SRB2149/SR-CRT/FPGA/SPI_to_CRT/src/gowin_dpb/gowin_dpb_tmp.v

//Copyright (C)2014-2024 Gowin Semiconductor Corporation.
//All rights reserved.
//File Title: Template file for instantiation
//Tool Version: V1.9.10.03 Education (64-bit)
//Part Number: GW1NR-LV9QN88PC6/I5
//Device: GW1NR-9
//Device Version: C
//Created Time: Sun May 10 15:20:16 2026

//Change the instance name and port connections to the signal names
//--------Copy here to design--------

    DPBSRAM your_instance_name(
        .douta(douta), //output [7:0] douta
        .doutb(doutb), //output [7:0] doutb
        .clka(clka), //input clka
        .ocea(ocea), //input ocea
        .cea(cea), //input cea
        .reseta(reseta), //input reseta
        .wrea(wrea), //input wrea
        .clkb(clkb), //input clkb
        .oceb(oceb), //input oceb
        .ceb(ceb), //input ceb
        .resetb(resetb), //input resetb
        .wreb(wreb), //input wreb
        .ada(ada), //input [14:0] ada
        .dina(dina), //input [7:0] dina
        .adb(adb), //input [14:0] adb
        .dinb(dinb) //input [7:0] dinb
    );

//--------Copy end-------------------
