SRB2149/SR-CRT/FPGA/CRT_Test/src/gowin_dpb/crt_frame_buffer_dpbsram.v

//Copyright (C)2014-2024 Gowin Semiconductor Corporation.
//All rights reserved.
//File Title: IP file
//Tool Version: V1.9.10.03 Education (64-bit)
//Part Number: GW1NR-LV9QN88PC6/I5
//Device: GW1NR-9
//Device Version: C
//Created Time: Mon Dec 15 19:14:27 2025

module CRT_FRAME_BUFFER_DPBSRAM (douta, doutb, clka, ocea, cea, reseta, wrea, clkb, oceb, ceb, resetb, wreb, ada, dina, adb, dinb);

output [7:0] douta;
output [7:0] doutb;
input clka;
input ocea;
input cea;
input reseta;
input wrea;
input clkb;
input oceb;
input ceb;
input resetb;
input wreb;
input [13:0] ada;
input [7:0] dina;
input [13:0] adb;
input [7:0] dinb;

wire [13:0] dpb_inst_0_douta_w;
wire [1:0] dpb_inst_0_douta;
wire [13:0] dpb_inst_0_doutb_w;
wire [1:0] dpb_inst_0_doutb;
wire [13:0] dpb_inst_1_douta_w;
wire [3:2] dpb_inst_1_douta;
wire [13:0] dpb_inst_1_doutb_w;
wire [3:2] dpb_inst_1_doutb;
wire [13:0] dpb_inst_2_douta_w;
wire [5:4] dpb_inst_2_douta;
wire [13:0] dpb_inst_2_doutb_w;
wire [5:4] dpb_inst_2_doutb;
wire [13:0] dpb_inst_3_douta_w;
wire [7:6] dpb_inst_3_douta;
wire [13:0] dpb_inst_3_doutb_w;
wire [7:6] dpb_inst_3_doutb;
wire [7:0] dpb_inst_4_douta_w;
wire [7:0] dpb_inst_4_douta;
wire [7:0] dpb_inst_4_doutb_w;
wire [7:0] dpb_inst_4_doutb;
wire dff_q_0;
wire dff_q_1;
wire cea_w;
wire ceb_w;
wire gw_gnd;

assign cea_w = ~wrea & cea;
assign ceb_w = ~wreb & ceb;
assign gw_gnd = 1'b0;

DPB dpb_inst_0 (
    .DOA({dpb_inst_0_douta_w[13:0],dpb_inst_0_douta[1:0]}),
    .DOB({dpb_inst_0_doutb_w[13:0],dpb_inst_0_doutb[1:0]}),
    .CLKA(clka),
    .OCEA(ocea),
    .CEA(cea),
    .RESETA(reseta),
    .WREA(wrea),
    .CLKB(clkb),
    .OCEB(oceb),
    .CEB(ceb),
    .RESETB(resetb),
    .WREB(wreb),
    .BLKSELA({gw_gnd,gw_gnd,ada[13]}),
    .BLKSELB({gw_gnd,gw_gnd,adb[13]}),
    .ADA({ada[12:0],gw_gnd}),
    .DIA({gw_gnd,gw_gnd,gw_gnd,gw_gnd,gw_gnd,gw_gnd,gw_gnd,gw_gnd,gw_gnd,gw_gnd,gw_gnd,gw_gnd,gw_gnd,gw_gnd,dina[1:0]}),
    .ADB({adb[12:0],gw_gnd}),
    .DIB({gw_gnd,gw_gnd,gw_gnd,gw_gnd,gw_gnd,gw_gnd,gw_gnd,gw_gnd,gw_gnd,gw_gnd,gw_gnd,gw_gnd,gw_gnd,gw_gnd,dinb[1:0]})
);

defparam dpb_inst_0.READ_MODE0 = 1'b0;
defparam dpb_inst_0.READ_MODE1 = 1'b0;
defparam dpb_inst_0.WRITE_MODE0 = 2'b00;
defparam dpb_inst_0.WRITE_MODE1 = 2'b00;
defparam dpb_inst_0.BIT_WIDTH_0 = 2;
defparam dpb_inst_0.BIT_WIDTH_1 = 2;
defparam dpb_inst_0.BLK_SEL_0 = 3'b000;
defparam dpb_inst_0.BLK_SEL_1 = 3'b000;
defparam dpb_inst_0.RESET_MODE = "ASYNC";
defparam dpb_inst_0.INIT_RAM_00 = 256'h000000004000000000000000001000000000000000000FFFFFFFFFFFFFFFFFFF;
defparam dpb_inst_0.INIT_RAM_01 = 256'h0000000000000000180000000000000000040000000000000000010000000000;
defparam dpb_inst_0.INIT_RAM_02 = 256'h0000001000000000000000000400000000000000000900000000000000000150;
defparam dpb_inst_0.INIT_RAM_03 = 256'h0000000000000004800000000000000001000000000000000000400000000000;
defparam dpb_inst_0.INIT_RAM_04 = 256'h0000040000000000000000010000000000000000084000000000000000011100;
defparam dpb_inst_0.INIT_RAM_05 = 256'h0000000000000108000000000000000040000000000000000010000000000000;
defparam dpb_inst_0.INIT_RAM_06 = 256'h0001000000000040000000400000000070000008100000000000000001041000;
defparam dpb_inst_0.INIT_RAM_07 = 256'h0010000000004080000000700000001000000000140000000400000000070000;
defparam dpb_inst_0.INIT_RAM_08 = 256'h00400000000F5800000010000000031E0000080400000000C780000101010000;
defparam dpb_inst_0.INIT_RAM_09 = 256'hFC0800000010080000070A0000000400000001E380000001000000007DE00000;
defparam dpb_inst_0.INIT_RAM_0A = 256'h10000000070E0000000400000001C28000000100000003F02000030040100000;
defparam dpb_inst_0.INIT_RAM_0B = 256'h1E0000400400800000C780000001000000003160000000400000001C78000000;
defparam dpb_inst_0.INIT_RAM_0C = 256'h0000000009000000010000000000800000004000000004000002001001000003;
defparam dpb_inst_0.INIT_RAM_0D = 256'h0000400100080000000000000040000000008000000010000000002000000004;
defparam dpb_inst_0.INIT_RAM_0E = 256'h0000000000000000400000000000000000100000000000000200040010000000;
defparam dpb_inst_0.INIT_RAM_0F = 256'h0040004000C00000000000001000000000000000000400000000000000000100;
defparam dpb_inst_0.INIT_RAM_10 = 256'h0000000000000010000000000000000004000000000000020001000000000000;
defparam dpb_inst_0.INIT_RAM_11 = 256'h400010000C002F40000000040000000BD0000000010000000000000000004000;
defparam dpb_inst_0.INIT_RAM_12 = 256'h0067CE0000000400000019F00000000100000006480002000040000001920000;
defparam dpb_inst_0.INIT_RAM_13 = 256'h00040000400BE080000001000020064820000000400000019208000000100000;
defparam dpb_inst_0.INIT_RAM_14 = 256'h000000000001000000000000000000400000000000020000100000002F8E0040;
defparam dpb_inst_0.INIT_RAM_15 = 256'h01000007FFFFFFF00000400003FFFFFFFC000010000000000000000004000000;
defparam dpb_inst_0.INIT_RAM_16 = 256'h00003000004000000000000C00001000003FFFFFFF00000400000FFFFFFFC000;
defparam dpb_inst_0.INIT_RAM_17 = 256'h4000007FFFFFFC000010000020000003000004000000000000C0000100000000;
defparam dpb_inst_0.INIT_RAM_18 = 256'h003C00041000000000000F00DD04000003FFFFFFC00001000000FFFFFFF00000;
defparam dpb_inst_0.INIT_RAM_19 = 256'h000007FFFFFF00DD04000003FFFFFFC00001000000000000F00CD04000000000;
defparam dpb_inst_0.INIT_RAM_1A = 256'h0F00CC04000000FFFFF3C00041000000000002F00EC04000000000007C000010;
defparam dpb_inst_0.INIT_RAM_1B = 256'h0000400003C00001000000200000F00CC04000000FFFFF3C0204100000000000;
defparam dpb_inst_0.INIT_RAM_1C = 256'hC00001000000000000F000104000000000023C00041000000000004F00050400;
defparam dpb_inst_0.INIT_RAM_1D = 256'h00040000F000004000000200003C00001000000000000F003404000000000003;
defparam dpb_inst_0.INIT_RAM_1E = 256'h00004003380000003C000010007E0000020F000004001F80000043C000010000;
defparam dpb_inst_0.INIT_RAM_1F = 256'h0040003C000010004E0020000F000004001380000003C00001000CE0000000F0;
defparam dpb_inst_0.INIT_RAM_20 = 256'h0010007E0000000F000004001F80000203C000010004E0000040F00000400138;
defparam dpb_inst_0.INIT_RAM_21 = 256'h04000F030004000000020003C0C001000000000000F030004000000000003C0C;
defparam dpb_inst_0.INIT_RAM_22 = 256'h04009080000003C0C001006F20000000F03000401BF80000C03C0C0010000000;
defparam dpb_inst_0.INIT_RAM_23 = 256'h5003C00001002C20002000F03000400B080000003C0C001002420000000F0300;
defparam dpb_inst_0.INIT_RAM_24 = 256'h0027E0000000F030004009C80000003C0C001002420000800F00000400908000;
defparam dpb_inst_0.INIT_RAM_25 = 256'h00F030004000000002003C0C001000000000000F030004000000000003C0C001;
defparam dpb_inst_0.INIT_RAM_26 = 256'h03FCC000003C0C001000000000000F030004000000008003C0C0010000000014;
defparam dpb_inst_0.INIT_RAM_27 = 256'h3C0000100CC03000300F0FFFC403300C000003C00001000FF3000000F0300040;
defparam dpb_inst_0.INIT_RAM_28 = 256'hC03000000F0FFC0407300C000003C3FF0103CFC3008000F055C040B3F0C01000;
defparam dpb_inst_0.INIT_RAM_29 = 256'h0FFCC4000000000103C3FF0101CCF3000080F0FFC040733CC000003C3FF3101C;
defparam dpb_inst_0.INIT_RAM_2A = 256'h00000003C15701003F30000000F0FFC0400FCC0080003C3FF01000000010000F;
defparam dpb_inst_0.INIT_RAM_2B = 256'h0001002C00000010F00000400B000000083C00001002000000000F0000040080;
defparam dpb_inst_0.INIT_RAM_2C = 256'h000000F00000400BC00000003C00001002000080000F000004008000100003C0;
defparam dpb_inst_0.INIT_RAM_2D = 256'h004000000000013C00001000000000008F000004000000000003C00001002F00;
defparam dpb_inst_0.INIT_RAM_2E = 256'h00003C00001000000000000F000004000000800003C00001000000100000F000;
defparam dpb_inst_0.INIT_RAM_2F = 256'h10000000F5B81F0000040000003D6E0BC00001000000000000F0000040000000;
defparam dpb_inst_0.INIT_RAM_30 = 256'h358F0000040000001D0D63C00001000000848158F000004000001120563C0000;
defparam dpb_inst_0.INIT_RAM_31 = 256'h000000320D61C00001000000048058F000004000000120163C00001000000074;
defparam dpb_inst_0.INIT_RAM_32 = 256'h00C000010000000000003000004000008000000C000010000010C83583000004;
defparam dpb_inst_0.INIT_RAM_33 = 256'h00000000C01000004000000000300C0000100000000FCC0300000400000003F3;
defparam dpb_inst_0.INIT_RAM_34 = 256'h000000400000000030000000100000800F0C0000000400001003C30000000100;
defparam dpb_inst_0.INIT_RAM_35 = 256'h00000000010000100000000F0C0080000400000003C3000000010000000000C0;
defparam dpb_inst_0.INIT_RAM_36 = 256'h0000100000000000000000040000800000000000010000100000000000004000;
defparam dpb_inst_0.INIT_RAM_37 = 256'h0000000010000400000000000008000100000000000000000040000000000000;
defparam dpb_inst_0.INIT_RAM_38 = 256'h000400000079E780000001000000000000000000400030000000000000100000;
defparam dpb_inst_0.INIT_RAM_39 = 256'h4D30C0010001000000238C3000800040000008E30C00000010000001E79E0000;
defparam dpb_inst_0.INIT_RAM_3A = 256'h01000000030C3000000040000000C30C0000001000300134C300000004000000;
defparam dpb_inst_0.INIT_RAM_3B = 256'h0C1000100040000000C30C0008001000000030C3000000040000000C30C00000;
defparam dpb_inst_0.INIT_RAM_3C = 256'h4000000041000000001000000010410000000400200004104000000100040003;
defparam dpb_inst_0.INIT_RAM_3D = 256'h3C00010010000000000000008004000000000000000001000000000000000000;
defparam dpb_inst_0.INIT_RAM_3E = 256'h000000086C00000004000000021B000000010020000F3CF000000040040003CF;
defparam dpb_inst_0.INIT_RAM_3F = 256'h00000004000000233F00000C0100000000CFC00000004000000023B000000010;

DPB dpb_inst_1 (
    .DOA({dpb_inst_1_douta_w[13:0],dpb_inst_1_douta[3:2]}),
    .DOB({dpb_inst_1_doutb_w[13:0],dpb_inst_1_doutb[3:2]}),
    .CLKA(clka),
    .OCEA(ocea),
    .CEA(cea),
    .RESETA(reseta),
    .WREA(wrea),
    .CLKB(clkb),
    .OCEB(oceb),
    .CEB(ceb),
    .RESETB(resetb),
    .WREB(wreb),
    .BLKSELA({gw_gnd,gw_gnd,ada[13]}),
    .BLKSELB({gw_gnd,gw_gnd,adb[13]}),
    .ADA({ada[12:0],gw_gnd}),
    .DIA({gw_gnd,gw_gnd,gw_gnd,gw_gnd,gw_gnd,gw_gnd,gw_gnd,gw_gnd,gw_gnd,gw_gnd,gw_gnd,gw_gnd,gw_gnd,gw_gnd,dina[3:2]}),
    .ADB({adb[12:0],gw_gnd}),
    .DIB({gw_gnd,gw_gnd,gw_gnd,gw_gnd,gw_gnd,gw_gnd,gw_gnd,gw_gnd,gw_gnd,gw_gnd,gw_gnd,gw_gnd,gw_gnd,gw_gnd,dinb[3:2]})
);

defparam dpb_inst_1.READ_MODE0 = 1'b0;
defparam dpb_inst_1.READ_MODE1 = 1'b0;
defparam dpb_inst_1.WRITE_MODE0 = 2'b00;
defparam dpb_inst_1.WRITE_MODE1 = 2'b00;
defparam dpb_inst_1.BIT_WIDTH_0 = 2;
defparam dpb_inst_1.BIT_WIDTH_1 = 2;
defparam dpb_inst_1.BLK_SEL_0 = 3'b000;
defparam dpb_inst_1.BLK_SEL_1 = 3'b000;
defparam dpb_inst_1.RESET_MODE = "ASYNC";
defparam dpb_inst_1.INIT_RAM_00 = 256'h0000000080000000000000000010000000000000000003FFFFFFFFFFFFFFFFFF;
defparam dpb_inst_1.INIT_RAM_01 = 256'h0000000000000000000000000000000000010000000000000000008000000000;
defparam dpb_inst_1.INIT_RAM_02 = 256'h0000008000000000000000001000000000000000000000000000000000000000;
defparam dpb_inst_1.INIT_RAM_03 = 256'h0000000000000000000000000000000000100000000000000000080000000000;
defparam dpb_inst_1.INIT_RAM_04 = 256'h0000000000000000000000300000000000000000000000000000000000000000;
defparam dpb_inst_1.INIT_RAM_05 = 256'h0000000000000000000000000000000001000000000000000000800000000000;
defparam dpb_inst_1.INIT_RAM_06 = 256'h0000000000000000000020000000000030000004000000000000000000000000;
defparam dpb_inst_1.INIT_RAM_07 = 256'h0000300000000000000000380000000010000000080000000008000000030000;
defparam dpb_inst_1.INIT_RAM_08 = 256'h0000000000008400002000000000000D000004000000000003C0000000000000;
defparam dpb_inst_1.INIT_RAM_09 = 256'hF3B40000000000000000ED000000000100000039400000000080000006100000;
defparam dpb_inst_1.INIT_RAM_0A = 256'h0000000000E500002000000000003B4000040000000003CED000000000000000;
defparam dpb_inst_1.INIT_RAM_0B = 256'h0F00000000000000000340000000001000000E10000000000800000384000000;
defparam dpb_inst_1.INIT_RAM_0C = 256'h00000000020000200000000000036000040000000000000C0000000000000000;
defparam dpb_inst_1.INIT_RAM_0D = 256'h0000000000000000038000000000010000002000000000008000000800000000;
defparam dpb_inst_1.INIT_RAM_0E = 256'h0000000000002000000000000000000400000000000000000000000000000000;
defparam dpb_inst_1.INIT_RAM_0F = 256'h0000000000000000000000000000100000000000000000080000000000000000;
defparam dpb_inst_1.INIT_RAM_10 = 256'h0000000000200000000000000000040000000000000000000000000000000000;
defparam dpb_inst_1.INIT_RAM_11 = 256'h0000000000003D00000000000001000F40000000000000800000000000000000;
defparam dpb_inst_1.INIT_RAM_12 = 256'h00116B0020000000000004580004000000000001260000000000000000498000;
defparam dpb_inst_1.INIT_RAM_13 = 256'h00000000000FDA000000000000100126B00000000000080049A0000000000000;
defparam dpb_inst_1.INIT_RAM_14 = 256'h000000200000000000000000040000000000000000000000000000003F6B0000;
defparam dpb_inst_1.INIT_RAM_15 = 256'h00000003FFFFFFF00000000000FFFFFFFC0000000000C0000000000000000000;
defparam dpb_inst_1.INIT_RAM_16 = 256'h00002000000000000000000400000000003FFFFFFF00000000000FFFFFFFC000;
defparam dpb_inst_1.INIT_RAM_17 = 256'h0000003FFFFFF000000000000000000000000000000C00000000000000000000;
defparam dpb_inst_1.INIT_RAM_18 = 256'h0020000400000000000004007700000003FFFFFF000000000000FFFFFFC00000;
defparam dpb_inst_1.INIT_RAM_19 = 256'h000003FFFFF0007400000000FFFFFC0015000000004000000007700000002000;
defparam dpb_inst_1.INIT_RAM_1A = 256'h10002400000000FFFFFC00000000000000000000037000000000000000000000;
defparam dpb_inst_1.INIT_RAM_1B = 256'h000000000400000000000000000100024000000007FFFF400090000000020000;
defparam dpb_inst_1.INIT_RAM_1C = 256'h00014000000000000D0000D000000000000040001400000000000010000D0000;
defparam dpb_inst_1.INIT_RAM_1D = 256'h0000000100000000000000000040000000000000400010001D00000000200004;
defparam dpb_inst_1.INIT_RAM_1E = 256'h000000019C000008400000000017000001100000000005C00000040000000000;
defparam dpb_inst_1.INIT_RAM_1F = 256'h0000004000000000E7000000100000000039C004000400000000067002000100;
defparam dpb_inst_1.INIT_RAM_20 = 256'h00000017000008100000000005C0000104000000000A7000000100000000029C;
defparam dpb_inst_1.INIT_RAM_21 = 256'h00001000C000000000000004003000000000004001000C000000000020004003;
defparam dpb_inst_1.INIT_RAM_22 = 256'h00004900000804003000003D40000101000C00000F5C00000040030000000000;
defparam dpb_inst_1.INIT_RAM_23 = 256'h0004000000003E40000001000C00000F900004004003000001240002001000C0;
defparam dpb_inst_1.INIT_RAM_24 = 256'h001170000801000C000004500001004003000001240000001000000000490000;
defparam dpb_inst_1.INIT_RAM_25 = 256'h01000C000000000000004003000000000000401000E000000000002004003000;
defparam dpb_inst_1.INIT_RAM_26 = 256'hC0F3C008004003000000000001001000E0000000000000040030000000000000;
defparam dpb_inst_1.INIT_RAM_27 = 256'h400000003300000000100FFFC00CC0000004040000000303CF000201000C0000;
defparam dpb_inst_1.INIT_RAM_28 = 256'h0C0008001000030000C3000100040000C00133C0000001000030004CF0000000;
defparam dpb_inst_1.INIT_RAM_29 = 256'h0003000000000000040000C0003CCF000041000030000F33C0002040000C0003;
defparam dpb_inst_1.INIT_RAM_2A = 256'h800800040000C0003CF0010001000030000F3C00000040000C00000000000010;
defparam dpb_inst_1.INIT_RAM_2B = 256'h0000001CE000000100000000073800000440000000010E000002100000000043;
defparam dpb_inst_1.INIT_RAM_2C = 256'h0800010000000007380100004000000001CE0000001000000000738000000400;
defparam dpb_inst_1.INIT_RAM_2D = 256'h0000000000000040000000000000000010000000000000000034000000001CE0;
defparam dpb_inst_1.INIT_RAM_2E = 256'h0000400000000000010000100000000000000000040000000000000000010000;
defparam dpb_inst_1.INIT_RAM_2F = 256'h00000000D2F48000000000000034BD2000000000000000000300000000000008;
defparam dpb_inst_1.INIT_RAM_30 = 256'h3AC80000000000010C8EB00000000000000260A4000000000000009829000000;
defparam dpb_inst_1.INIT_RAM_31 = 256'h000000398E900000000000000260A40000000000000098291000000000000832;
defparam dpb_inst_1.INIT_RAM_32 = 256'h0080000000000300000000000000000000000000000000000000E63A40000000;
defparam dpb_inst_1.INIT_RAM_33 = 256'h0000000000000000000000000000000000000000000F3C0100000000000003CF;
defparam dpb_inst_1.INIT_RAM_34 = 256'h080000000003000C00000000000000000F000000000000000003C00000000000;
defparam dpb_inst_1.INIT_RAM_35 = 256'h00000000000000000000000F0C0000000000000003C300100000000000003000;
defparam dpb_inst_1.INIT_RAM_36 = 256'h8000000002000000000000000000400000000000000000000000000000000000;
defparam dpb_inst_1.INIT_RAM_37 = 256'h0000000000000000000000000000000000000000000001000000000000000000;
defparam dpb_inst_1.INIT_RAM_38 = 256'h00000002003CF3C0000000000040000000000000000000000000000000000000;
defparam dpb_inst_1.INIT_RAM_39 = 256'h0C30C0000000000000030C3000000000000000C30C00100000000000F3CF0008;
defparam dpb_inst_1.INIT_RAM_3A = 256'h0000020001041000000000004000C3040000000000000030C300000000000000;
defparam dpb_inst_1.INIT_RAM_3B = 256'h0000000000000000000000000000000000000000000100000000000410400080;
defparam dpb_inst_1.INIT_RAM_3C = 256'h0002000000020000000000400000000000000000000000000000000000000000;
defparam dpb_inst_1.INIT_RAM_3D = 256'hDE000000000000008A20C0000000000000228830001000000000008208000800;
defparam dpb_inst_1.INIT_RAM_3E = 256'h0200008C3C00000000004000230F0000000000000007DF7800000000000001F7;
defparam dpb_inst_1.INIT_RAM_3F = 256'h00000000000000031C0000000000000004C3400001000000000130D000008000;

DPB dpb_inst_2 (
    .DOA({dpb_inst_2_douta_w[13:0],dpb_inst_2_douta[5:4]}),
    .DOB({dpb_inst_2_doutb_w[13:0],dpb_inst_2_doutb[5:4]}),
    .CLKA(clka),
    .OCEA(ocea),
    .CEA(cea),
    .RESETA(reseta),
    .WREA(wrea),
    .CLKB(clkb),
    .OCEB(oceb),
    .CEB(ceb),
    .RESETB(resetb),
    .WREB(wreb),
    .BLKSELA({gw_gnd,gw_gnd,ada[13]}),
    .BLKSELB({gw_gnd,gw_gnd,adb[13]}),
    .ADA({ada[12:0],gw_gnd}),
    .DIA({gw_gnd,gw_gnd,gw_gnd,gw_gnd,gw_gnd,gw_gnd,gw_gnd,gw_gnd,gw_gnd,gw_gnd,gw_gnd,gw_gnd,gw_gnd,gw_gnd,dina[5:4]}),
    .ADB({adb[12:0],gw_gnd}),
    .DIB({gw_gnd,gw_gnd,gw_gnd,gw_gnd,gw_gnd,gw_gnd,gw_gnd,gw_gnd,gw_gnd,gw_gnd,gw_gnd,gw_gnd,gw_gnd,gw_gnd,dinb[5:4]})
);

defparam dpb_inst_2.READ_MODE0 = 1'b0;
defparam dpb_inst_2.READ_MODE1 = 1'b0;
defparam dpb_inst_2.WRITE_MODE0 = 2'b00;
defparam dpb_inst_2.WRITE_MODE1 = 2'b00;
defparam dpb_inst_2.BIT_WIDTH_0 = 2;
defparam dpb_inst_2.BIT_WIDTH_1 = 2;
defparam dpb_inst_2.BLK_SEL_0 = 3'b000;
defparam dpb_inst_2.BLK_SEL_1 = 3'b000;
defparam dpb_inst_2.RESET_MODE = "ASYNC";
defparam dpb_inst_2.INIT_RAM_00 = 256'h0000000060000000000000000000000000000000000003FFFFFFFFFFFFFFFFFF;
defparam dpb_inst_2.INIT_RAM_01 = 256'h0000000000000000000000000000000000000000000000000000024000000000;
defparam dpb_inst_2.INIT_RAM_02 = 256'h0000004200000000000000000000000000000000000000000000000000000000;
defparam dpb_inst_2.INIT_RAM_03 = 256'h0000000000000000000000000000000000000000000000000002040000000000;
defparam dpb_inst_2.INIT_RAM_04 = 256'h0000403000000000000000000000000000000000000000000000000000000000;
defparam dpb_inst_2.INIT_RAM_05 = 256'h0000000000000000000000000000000000000000000000000200000000000000;
defparam dpb_inst_2.INIT_RAM_06 = 256'h0040010000000080000000008000000020000000000000000000000000000000;
defparam dpb_inst_2.INIT_RAM_07 = 256'h0000100000000000000000240000000000000000000000020000000000020000;
defparam dpb_inst_2.INIT_RAM_08 = 256'h4000100000C04000000000080000000C00000000000000000300000000000000;
defparam dpb_inst_2.INIT_RAM_09 = 256'hCC50000000000000003030000000000000000C0C000002000000000303000000;
defparam dpb_inst_2.INIT_RAM_0A = 256'h000100003010000000000080000C040000000000000003314000000000000000;
defparam dpb_inst_2.INIT_RAM_0B = 256'h0C0000000000000000030000000000000003010000020000000000C040000040;
defparam dpb_inst_2.INIT_RAM_0C = 256'h0010000006000000000008000000100000000000000000040000000000000000;
defparam dpb_inst_2.INIT_RAM_0D = 256'h0000000000000000000000000000000000006000020000000000001000004000;
defparam dpb_inst_2.INIT_RAM_0E = 256'h0100000000000000000080000000000000000000000000000000000000000000;
defparam dpb_inst_2.INIT_RAM_0F = 256'h0000000000000000000000000000000000000002000000000000000000400000;
defparam dpb_inst_2.INIT_RAM_10 = 256'h1000000000000000000800000000000000000000000000000000000000000000;
defparam dpb_inst_2.INIT_RAM_11 = 256'h0000000000003CA0000000000000000F28000200000000000000000040000000;
defparam dpb_inst_2.INIT_RAM_12 = 256'h0000BC80000000000080002C0000000000000000190000000000000000064000;
defparam dpb_inst_2.INIT_RAM_13 = 256'h00000000000F645000000000000000190C020000000000000645004000000001;
defparam dpb_inst_2.INIT_RAM_14 = 256'h000000000000000008000000000000000000000000000000000000003D9D4000;
defparam dpb_inst_2.INIT_RAM_15 = 256'h00000003FFFFFFF00000000000FFFFFFFC000000000000000000C00000000010;
defparam dpb_inst_2.INIT_RAM_16 = 256'h00000000000000008000000000000000003FFFFFFF00000000000FFFFFFFC000;
defparam dpb_inst_2.INIT_RAM_17 = 256'h0000003FFFFFF0000000000000000000000000000000000000C0000000000100;
defparam dpb_inst_2.INIT_RAM_18 = 256'h001001A80000000800000000F780000003FFFFFF000000000000FFFFFFC00000;
defparam dpb_inst_2.INIT_RAM_19 = 256'h000003FFFFF000F680000000FFFFFC0012A0000000000000800F380000001000;
defparam dpb_inst_2.INIT_RAM_1A = 256'h10000100000000FFFFFC0004A00000000000000001F000000000000000000000;
defparam dpb_inst_2.INIT_RAM_1B = 256'h000000000800000000000000000200001000000003FFFF800006000000000000;
defparam dpb_inst_2.INIT_RAM_1C = 256'h0000A00000000C000200034800000000000080004A00000000000020003D8000;
defparam dpb_inst_2.INIT_RAM_1D = 256'h00000002000000000000000000800000000000000000A0003D80000000000018;
defparam dpb_inst_2.INIT_RAM_1E = 256'h000000026C004000800000000083002000200000000020C00000080000000000;
defparam dpb_inst_2.INIT_RAM_1F = 256'h00000080000000009B000000200000000026C00000880000000009B000001200;
defparam dpb_inst_2.INIT_RAM_20 = 256'h00000083000400200000000020C0020008000000000DB000000200000000036C;
defparam dpb_inst_2.INIT_RAM_21 = 256'h0000200C000000000000000803000000000000008200C0000000000000108030;
defparam dpb_inst_2.INIT_RAM_22 = 256'h00000600004008030000003C0000200200C000000F0C00000080300000000000;
defparam dpb_inst_2.INIT_RAM_23 = 256'h000800000000358000000200C000000D60000080803000000018000010200C00;
defparam dpb_inst_2.INIT_RAM_24 = 256'h00003000040200C0000000000002008030000000180000002000000000060000;
defparam dpb_inst_2.INIT_RAM_25 = 256'h0200C200000000000000803040000000000080200C0000000000001008030000;
defparam dpb_inst_2.INIT_RAM_26 = 256'h3CCFC00040803000000000000020200C00000000000000080304000000000000;
defparam dpb_inst_2.INIT_RAM_27 = 256'h800000000C33800000200FFFF0030CE000800800000000F33F00100200C00000;
defparam dpb_inst_2.INIT_RAM_28 = 256'h00800004200FFCC000002000020803FF3000B33800000200EA8C002CCE000000;
defparam dpb_inst_2.INIT_RAM_29 = 256'h0FFCE000000000000803FF30000C3F00800200FFCC00030FC01000803FF38000;
defparam dpb_inst_2.INIT_RAM_2A = 256'h4000004803AA300033F000002200FFCC000CFC000000803FF300000000000020;
defparam dpb_inst_2.INIT_RAM_2B = 256'h00000003D00000020000000000F400800080000000003100100020000000000C;
defparam dpb_inst_2.INIT_RAM_2C = 256'h0000060000000000F40000028000000000010000002000000000004000000800;
defparam dpb_inst_2.INIT_RAM_2D = 256'h00000000000000800000000000000000200000000000003000080000000003D0;
defparam dpb_inst_2.INIT_RAM_2E = 256'h0000400000000000000000200000000000000000080000000000000000020000;
defparam dpb_inst_2.INIT_RAM_2F = 256'h0000000043F2C000000000000010FCB000000000000030000000000000000000;
defparam dpb_inst_2.INIT_RAM_30 = 256'hF5C400000000000026FD72000000000000099C50000000000000026714000000;
defparam dpb_inst_2.INIT_RAM_31 = 256'h000000167D40000000000000099E50000000000000226794000000000000049B;
defparam dpb_inst_2.INIT_RAM_32 = 256'h000000000000000000003000000000000000000000000000000059F500000000;
defparam dpb_inst_2.INIT_RAM_33 = 256'h0000000E00000000000000000380000000000000200CFC00000000000004033F;
defparam dpb_inst_2.INIT_RAM_34 = 256'h000000000000003380030000000000000CEC00000000000000033B0000000000;
defparam dpb_inst_2.INIT_RAM_35 = 256'h00000000000000000000000CEC00000000000020033B0000000000000400CE00;
defparam dpb_inst_2.INIT_RAM_36 = 256'h0000000000000000001000000000000000000800000000000000000000000000;
defparam dpb_inst_2.INIT_RAM_37 = 256'h0000000000000000000000000000000000002000000000000000000400000000;
defparam dpb_inst_2.INIT_RAM_38 = 256'h00000000003CF3C0010000000000000000008000000000000000000000000000;
defparam dpb_inst_2.INIT_RAM_39 = 256'h00000000000000000001041000000000002000410400000000000400F3CF0000;
defparam dpb_inst_2.INIT_RAM_3A = 256'h0000000000000000100000000000000000080000000000000000000000000000;
defparam dpb_inst_2.INIT_RAM_3B = 256'hA20C000000000000002082000000000020000820800000000004000000000000;
defparam dpb_inst_2.INIT_RAM_3C = 256'h0000000134C3000100000000008E30C0008000000000238C3000000000000008;
defparam dpb_inst_2.INIT_RAM_3D = 256'hCF000000000000000C30C0000000002000030C3000000000040004D30C000000;
defparam dpb_inst_2.INIT_RAM_3E = 256'h0000000C3000001000000000030C0000080000000003CF3C00000000000000F3;
defparam dpb_inst_2.INIT_RAM_3F = 256'h000000000000000104800000000020000041000000000004000030C000000000;

DPB dpb_inst_3 (
    .DOA({dpb_inst_3_douta_w[13:0],dpb_inst_3_douta[7:6]}),
    .DOB({dpb_inst_3_doutb_w[13:0],dpb_inst_3_doutb[7:6]}),
    .CLKA(clka),
    .OCEA(ocea),
    .CEA(cea),
    .RESETA(reseta),
    .WREA(wrea),
    .CLKB(clkb),
    .OCEB(oceb),
    .CEB(ceb),
    .RESETB(resetb),
    .WREB(wreb),
    .BLKSELA({gw_gnd,gw_gnd,ada[13]}),
    .BLKSELB({gw_gnd,gw_gnd,adb[13]}),
    .ADA({ada[12:0],gw_gnd}),
    .DIA({gw_gnd,gw_gnd,gw_gnd,gw_gnd,gw_gnd,gw_gnd,gw_gnd,gw_gnd,gw_gnd,gw_gnd,gw_gnd,gw_gnd,gw_gnd,gw_gnd,dina[7:6]}),
    .ADB({adb[12:0],gw_gnd}),
    .DIB({gw_gnd,gw_gnd,gw_gnd,gw_gnd,gw_gnd,gw_gnd,gw_gnd,gw_gnd,gw_gnd,gw_gnd,gw_gnd,gw_gnd,gw_gnd,gw_gnd,dinb[7:6]})
);

defparam dpb_inst_3.READ_MODE0 = 1'b0;
defparam dpb_inst_3.READ_MODE1 = 1'b0;
defparam dpb_inst_3.WRITE_MODE0 = 2'b00;
defparam dpb_inst_3.WRITE_MODE1 = 2'b00;
defparam dpb_inst_3.BIT_WIDTH_0 = 2;
defparam dpb_inst_3.BIT_WIDTH_1 = 2;
defparam dpb_inst_3.BLK_SEL_0 = 3'b000;
defparam dpb_inst_3.BLK_SEL_1 = 3'b000;
defparam dpb_inst_3.RESET_MODE = "ASYNC";
defparam dpb_inst_3.INIT_RAM_00 = 256'h000000002000000000000000000C000000000000000003FFFFFFFFFFFFFFFFFF;
defparam dpb_inst_3.INIT_RAM_01 = 256'h0000000000000000280000000000000000060000000000000000008000000000;
defparam dpb_inst_3.INIT_RAM_02 = 256'h00000008000000000000000002400000000000000000A0000000000000000020;
defparam dpb_inst_3.INIT_RAM_03 = 256'h0000000000000022000000000000000004800000000000000000200000000000;
defparam dpb_inst_3.INIT_RAM_04 = 256'h0000020000000000000000008400000000000000002200000000000000000800;
defparam dpb_inst_3.INIT_RAM_05 = 256'h0000000000002080000000000000000420000000000000000008000000000000;
defparam dpb_inst_3.INIT_RAM_06 = 256'h0000800000000000000000204000000030000000082000000000000000020000;
defparam dpb_inst_3.INIT_RAM_07 = 256'h000C000000202000000003300000040800000000000000000200000000030000;
defparam dpb_inst_3.INIT_RAM_08 = 256'h002000000030E800000008040000000E00000002020000002380000000800000;
defparam dpb_inst_3.INIT_RAM_09 = 256'h3C00000020080000000E000000040200000003840000000080000000E3A00000;
defparam dpb_inst_3.INIT_RAM_0A = 256'h0800000002000000000200000000800000000080300000F00000000020000000;
defparam dpb_inst_3.INIT_RAM_0B = 256'h8E000020020000000003800004008000000000A0000000200000000828000000;
defparam dpb_inst_3.INIT_RAM_0C = 256'h000000000380000000800000000C200000002001000003000000000800800000;
defparam dpb_inst_3.INIT_RAM_0D = 256'h0000200080000000002000040020000000003800000008000000000200000002;
defparam dpb_inst_3.INIT_RAM_0E = 256'h0000000000000000200000000000000000080010000000000000020008000000;
defparam dpb_inst_3.INIT_RAM_0F = 256'h000000200000000000000C000800000000000000000200000000000000000080;
defparam dpb_inst_3.INIT_RAM_10 = 256'h0000000000000008000000000000000002000100000000000000800080000000;
defparam dpb_inst_3.INIT_RAM_11 = 256'h00000800000016F0000C000200000005BC000000008000000000000000002000;
defparam dpb_inst_3.INIT_RAM_12 = 256'h0022F34000000200000008BC0000000080001002240000000020000800890000;
defparam dpb_inst_3.INIT_RAM_13 = 256'h000200000005B16008000080000002245C010000200000008916000000080000;
defparam dpb_inst_3.INIT_RAM_14 = 256'h0000000000008000000000000000002000010000000000000800008016C38000;
defparam dpb_inst_3.INIT_RAM_15 = 256'h00800003FFFFFFFC0000200000FFFFFFFF000008000000000000000002000000;
defparam dpb_inst_3.INIT_RAM_16 = 256'h00000C00002000000000000300000800001FFFFFFFC0000200000FFFFFFFF000;
defparam dpb_inst_3.INIT_RAM_17 = 256'h2000003FFFFFFB000008000000000001C0000200000000000030000080000000;
defparam dpb_inst_3.INIT_RAM_18 = 256'h000B00A808000000000002C0E2C2000001FFFFFFB00000800000FFFFFFEC0000;
defparam dpb_inst_3.INIT_RAM_19 = 256'h000003FFFFFEC0E2C2000000FFFFFFB022808000000000002C0E6C2000000000;
defparam dpb_inst_3.INIT_RAM_1A = 256'h0EC036020000003FFFFFB006B0800000100000EC03E02000000800003B000008;
defparam dpb_inst_3.INIT_RAM_1B = 256'h000000000BB00000800000000001EC036020000003FFFFFB0053080000000000;
defparam dpb_inst_3.INIT_RAM_1C = 256'hB00A80800000000000EC039C2000000100003B00280800000080000EC038C200;
defparam dpb_inst_3.INIT_RAM_1D = 256'h00000008EC00002000000000013B00000800000000000EC03802000000000003;
defparam dpb_inst_3.INIT_RAM_1E = 256'h000020019C0000003B000008006B0010000EC00002001AC0080003B000008000;
defparam dpb_inst_3.INIT_RAM_1F = 256'h0000083B00000800670000010EC000020019C0000003B00000800670000000EC;
defparam dpb_inst_3.INIT_RAM_20 = 256'h0008006B0000000EC00002001AC0010003B00000800670008000EC000020019C;
defparam dpb_inst_3.INIT_RAM_21 = 256'h00080EC30002000000000103B0C000800000000000EC30002000000000003B0C;
defparam dpb_inst_3.INIT_RAM_22 = 256'h02000900000003B0C000803680000000EC3000200DAC000C003B0C0008000000;
defparam dpb_inst_3.INIT_RAM_23 = 256'h2803B00000801240000100EC30002004900000003B0C000800240000000EC300;
defparam dpb_inst_3.INIT_RAM_24 = 256'h8002B0000000EC30002000A00000003B0C000800240000400EC0000200090000;
defparam dpb_inst_3.INIT_RAM_25 = 256'h00EC30002000000001003B0C400800000000000EC32002000000000003B0C000;
defparam dpb_inst_3.INIT_RAM_26 = 256'h0C3F0000003B0C000800000000000EC32002000000000403B0C400800000000A;
defparam dpb_inst_3.INIT_RAM_27 = 256'h3B000008000C7003000EC7FFF200031C000003B000008030FC000000EC300020;
defparam dpb_inst_3.INIT_RAM_28 = 256'h0C7000000EC0000202031C000003B0FF0080F0F7000040EC3FC0201C3DC00020;
defparam dpb_inst_3.INIT_RAM_29 = 256'hC00032000000020003B00000808CFC004000EC000020233F0000003B0000C808;
defparam dpb_inst_3.INIT_RAM_2A = 256'h00000003B0FF00800FF0000000EC3FC02003FC0000043B00000800000000020E;
defparam dpb_inst_3.INIT_RAM_2B = 256'h00008003C0020000EC00002000F00040003B00000800000000000EC000020000;
defparam dpb_inst_3.INIT_RAM_2C = 256'h000000EC00002000F00000003B00000800000000004EC00002000000000023B0;
defparam dpb_inst_3.INIT_RAM_2D = 256'h002000000200003B00000800000040000EC00002000000000003B000008003C0;
defparam dpb_inst_3.INIT_RAM_2E = 256'h00003B00000800000000000EC00002000000000007B00000800000000002EC00;
defparam dpb_inst_3.INIT_RAM_2F = 256'h080000022BD94EC000020000004AF653B00000800000000000EC000020000000;
defparam dpb_inst_3.INIT_RAM_30 = 256'h1AC2C000020000001BC6B0B000008000000640A86C000020000001902A3B0000;
defparam dpb_inst_3.INIT_RAM_31 = 256'h0000020906A0B000008000004641282C000020000001904A0B0000080000006F;
defparam dpb_inst_3.INIT_RAM_32 = 256'h003000008000000000000C000020000000000007000008000000241A82C00002;
defparam dpb_inst_3.INIT_RAM_33 = 256'h00020031000C0000200000400C400300000800000003FC00C0000200000000FF;
defparam dpb_inst_3.INIT_RAM_34 = 256'h0000002000000000700000000800000003DC0040000200000000F70030000080;
defparam dpb_inst_3.INIT_RAM_35 = 256'h020000000000000800004003DC0000000200000000F7000000008000000001C0;
defparam dpb_inst_3.INIT_RAM_36 = 256'h0000080000000000000000020000000000000400008000000000000200002000;
defparam dpb_inst_3.INIT_RAM_37 = 256'h0000000000000200004000000000000080000000000000000020000000000000;
defparam dpb_inst_3.INIT_RAM_38 = 256'h00020000003CF3C0000000800000000000000000200000000000003000080002;
defparam dpb_inst_3.INIT_RAM_39 = 256'h02082000000080004000000000000020000000000000000008000000F3CF0000;
defparam dpb_inst_3.INIT_RAM_3A = 256'h0080000008E30C00000020000002288300000008000000082080030002000200;
defparam dpb_inst_3.INIT_RAM_3B = 256'hC30C0008002000400134C3000000080000004D30C0000002000000238C300000;
defparam dpb_inst_3.INIT_RAM_3C = 256'h2000000030C3000000080000000C30C0000002000000030C3000100080020000;
defparam dpb_inst_3.INIT_RAM_3D = 256'hCF000080080040000C3040000002000000030C1000000080000000C30C000000;
defparam dpb_inst_3.INIT_RAM_3E = 256'h000000003200000002000000000C8000000080000003CF3C00010020020000F3;
defparam dpb_inst_3.INIT_RAM_3F = 256'h0000080200C0000008C00000008000000003300000002000000000CC00000008;

DPB dpb_inst_4 (
    .DOA({dpb_inst_4_douta_w[7:0],dpb_inst_4_douta[7:0]}),
    .DOB({dpb_inst_4_doutb_w[7:0],dpb_inst_4_doutb[7:0]}),
    .CLKA(clka),
    .OCEA(ocea),
    .CEA(cea),
    .RESETA(reseta),
    .WREA(wrea),
    .CLKB(clkb),
    .OCEB(oceb),
    .CEB(ceb),
    .RESETB(resetb),
    .WREB(wreb),
    .BLKSELA({ada[13],ada[12],ada[11]}),
    .BLKSELB({adb[13],adb[12],adb[11]}),
    .ADA({ada[10:0],gw_gnd,gw_gnd,gw_gnd}),
    .DIA({gw_gnd,gw_gnd,gw_gnd,gw_gnd,gw_gnd,gw_gnd,gw_gnd,gw_gnd,dina[7:0]}),
    .ADB({adb[10:0],gw_gnd,gw_gnd,gw_gnd}),
    .DIB({gw_gnd,gw_gnd,gw_gnd,gw_gnd,gw_gnd,gw_gnd,gw_gnd,gw_gnd,dinb[7:0]})
);

defparam dpb_inst_4.READ_MODE0 = 1'b0;
defparam dpb_inst_4.READ_MODE1 = 1'b0;
defparam dpb_inst_4.WRITE_MODE0 = 2'b00;
defparam dpb_inst_4.WRITE_MODE1 = 2'b00;
defparam dpb_inst_4.BIT_WIDTH_0 = 8;
defparam dpb_inst_4.BIT_WIDTH_1 = 8;
defparam dpb_inst_4.BLK_SEL_0 = 3'b100;
defparam dpb_inst_4.BLK_SEL_1 = 3'b100;
defparam dpb_inst_4.RESET_MODE = "ASYNC";
defparam dpb_inst_4.INIT_RAM_00 = 256'h00000000004000000001800000000100000000000000000002001F00079F03E0;
defparam dpb_inst_4.INIT_RAM_01 = 256'h2000000001800000000200000000000000000002000F80078F83E00000000000;
defparam dpb_inst_4.INIT_RAM_02 = 256'h800000000400000000000000000001000F800F0F81F000000000000000000000;
defparam dpb_inst_4.INIT_RAM_03 = 256'h00000000000000000001000F800F0F81F0000000000000000000001000000001;
defparam dpb_inst_4.INIT_RAM_04 = 256'h00000000008007C01E07C0F80000000000000000000008000000018000000008;
defparam dpb_inst_4.INIT_RAM_05 = 256'h8007C01E07C0F800000000000000000000060000000180000000100000000000;
defparam dpb_inst_4.INIT_RAM_06 = 256'hE0F8000000000000000000000100000001800000006000000000000000000000;
defparam dpb_inst_4.INIT_RAM_07 = 256'h0000000000000000800000018000000080000000000000000000008003E03C03;
defparam dpb_inst_4.INIT_RAM_08 = 256'h000000400000018000000100000000000000000000004003E03C03E07C000000;
defparam dpb_inst_4.INIT_RAM_09 = 256'h00018000000200000000000000000000004003E03C03E07C0000000000000000;
defparam dpb_inst_4.INIT_RAM_0A = 256'h0400000000000000000000002001F07801F03E00000000000000000000002000;
defparam dpb_inst_4.INIT_RAM_0B = 256'h000000000000002001F07801F03E000000000000000000000010000001800000;
defparam dpb_inst_4.INIT_RAM_0C = 256'h00001FFFF0F000F01FFFE0000000000000000000080000018000000800000000;
defparam dpb_inst_4.INIT_RAM_0D = 256'hF000F01FFFE00000000000000000000600000180000010000000000000000000;
defparam dpb_inst_4.INIT_RAM_0E = 256'h00000000000000000000010000018000006000000000000000000000019FFFF0;
defparam dpb_inst_4.INIT_RAM_0F = 256'h0000000000008000018000008000000000000000000000038000000000000000;
defparam dpb_inst_4.INIT_RAM_10 = 256'h0040000180000100000000000000000000000700000000000000000000000000;
defparam dpb_inst_4.INIT_RAM_11 = 256'h000200000000000000000000000FFFFFFFFFFFFFFFFFFC000000000000000000;
defparam dpb_inst_4.INIT_RAM_12 = 256'h00000000000000001FFFFFFFFFFFFFFFFFFC0000000000000000000020000180;
defparam dpb_inst_4.INIT_RAM_13 = 256'h0000000000000000000000000000000000000000000000100001800004000000;
defparam dpb_inst_4.INIT_RAM_14 = 256'h0000000000000000000000000000000000000C00018000080000000000000000;
defparam dpb_inst_4.INIT_RAM_15 = 256'h0000000000000000000000000002000180003000000000000000000000000000;
defparam dpb_inst_4.INIT_RAM_16 = 256'h0000000000000000010001800040000000000000000000000000000000000000;
defparam dpb_inst_4.INIT_RAM_17 = 256'h0000000080018000800000000000000000000000000000000000000000000000;
defparam dpb_inst_4.INIT_RAM_18 = 256'h0180010000000000000000000000000000000000000000000000000000000000;
defparam dpb_inst_4.INIT_RAM_19 = 256'h0000000000000000000000000000000000000000000000000000000000000040;
defparam dpb_inst_4.INIT_RAM_1A = 256'h0000000000000000000000000000000000000000000000000000200180020000;
defparam dpb_inst_4.INIT_RAM_1B = 256'h0000000000000000000000000000000000000000001801800400000000000000;
defparam dpb_inst_4.INIT_RAM_1C = 256'h0000000000000000000000000000000004018018000000000000000000000000;
defparam dpb_inst_4.INIT_RAM_1D = 256'h0000000000000000000000020180200000000000000000000000000000000000;
defparam dpb_inst_4.INIT_RAM_1E = 256'h0000000000000101804000000000000000000000000000000000000000000000;
defparam dpb_inst_4.INIT_RAM_1F = 256'h0000818080000000000000000000000000000000000000000000000000000000;
defparam dpb_inst_4.INIT_RAM_20 = 256'h0000000000000000000000000000000000000000000000000000000000000000;
defparam dpb_inst_4.INIT_RAM_21 = 256'h0000000000000000000000000000000000000000000000000000000000418100;
defparam dpb_inst_4.INIT_RAM_22 = 256'h0000000000000000000000000000000000000000000000002182000000000000;
defparam dpb_inst_4.INIT_RAM_23 = 256'h0000000000000000000000000000000000000019840000000000000000000000;
defparam dpb_inst_4.INIT_RAM_24 = 256'h0000000000000000000000000000059800000000000000000000000000000000;
defparam dpb_inst_4.INIT_RAM_25 = 256'h00000000000000000003A0000000000000000000000000000000000000000000;
defparam dpb_inst_4.INIT_RAM_26 = 256'hFFFFFFFFFFC00000000000000000000000000000000000000000000000000000;
defparam dpb_inst_4.INIT_RAM_27 = 256'hFFFFFFFFFFFFFFFFFFFFFFFFFFFFFFFFFFFFFFFFFFFFFFFFFFFFFFFFFFFFFFFF;

DFFE dff_inst_0 (
  .Q(dff_q_0),
  .D(ada[13]),
  .CLK(clka),
  .CE(cea_w)
);
DFFE dff_inst_1 (
  .Q(dff_q_1),
  .D(adb[13]),
  .CLK(clkb),
  .CE(ceb_w)
);
MUX2 mux_inst_4 (
  .O(douta[0]),
  .I0(dpb_inst_0_douta[0]),
  .I1(dpb_inst_4_douta[0]),
  .S0(dff_q_0)
);
MUX2 mux_inst_9 (
  .O(douta[1]),
  .I0(dpb_inst_0_douta[1]),
  .I1(dpb_inst_4_douta[1]),
  .S0(dff_q_0)
);
MUX2 mux_inst_14 (
  .O(douta[2]),
  .I0(dpb_inst_1_douta[2]),
  .I1(dpb_inst_4_douta[2]),
  .S0(dff_q_0)
);
MUX2 mux_inst_19 (
  .O(douta[3]),
  .I0(dpb_inst_1_douta[3]),
  .I1(dpb_inst_4_douta[3]),
  .S0(dff_q_0)
);
MUX2 mux_inst_24 (
  .O(douta[4]),
  .I0(dpb_inst_2_douta[4]),
  .I1(dpb_inst_4_douta[4]),
  .S0(dff_q_0)
);
MUX2 mux_inst_29 (
  .O(douta[5]),
  .I0(dpb_inst_2_douta[5]),
  .I1(dpb_inst_4_douta[5]),
  .S0(dff_q_0)
);
MUX2 mux_inst_34 (
  .O(douta[6]),
  .I0(dpb_inst_3_douta[6]),
  .I1(dpb_inst_4_douta[6]),
  .S0(dff_q_0)
);
MUX2 mux_inst_39 (
  .O(douta[7]),
  .I0(dpb_inst_3_douta[7]),
  .I1(dpb_inst_4_douta[7]),
  .S0(dff_q_0)
);
MUX2 mux_inst_44 (
  .O(doutb[0]),
  .I0(dpb_inst_0_doutb[0]),
  .I1(dpb_inst_4_doutb[0]),
  .S0(dff_q_1)
);
MUX2 mux_inst_49 (
  .O(doutb[1]),
  .I0(dpb_inst_0_doutb[1]),
  .I1(dpb_inst_4_doutb[1]),
  .S0(dff_q_1)
);
MUX2 mux_inst_54 (
  .O(doutb[2]),
  .I0(dpb_inst_1_doutb[2]),
  .I1(dpb_inst_4_doutb[2]),
  .S0(dff_q_1)
);
MUX2 mux_inst_59 (
  .O(doutb[3]),
  .I0(dpb_inst_1_doutb[3]),
  .I1(dpb_inst_4_doutb[3]),
  .S0(dff_q_1)
);
MUX2 mux_inst_64 (
  .O(doutb[4]),
  .I0(dpb_inst_2_doutb[4]),
  .I1(dpb_inst_4_doutb[4]),
  .S0(dff_q_1)
);
MUX2 mux_inst_69 (
  .O(doutb[5]),
  .I0(dpb_inst_2_doutb[5]),
  .I1(dpb_inst_4_doutb[5]),
  .S0(dff_q_1)
);
MUX2 mux_inst_74 (
  .O(doutb[6]),
  .I0(dpb_inst_3_doutb[6]),
  .I1(dpb_inst_4_doutb[6]),
  .S0(dff_q_1)
);
MUX2 mux_inst_79 (
  .O(doutb[7]),
  .I0(dpb_inst_3_doutb[7]),
  .I1(dpb_inst_4_doutb[7]),
  .S0(dff_q_1)
);
endmodule //CRT_FRAME_BUFFER_DPBSRAM
